jeroen94704/TeensyDSPDAC/dac1.kicad_sch

## KiCad design dac1.kicad_sch (2023-10-21)

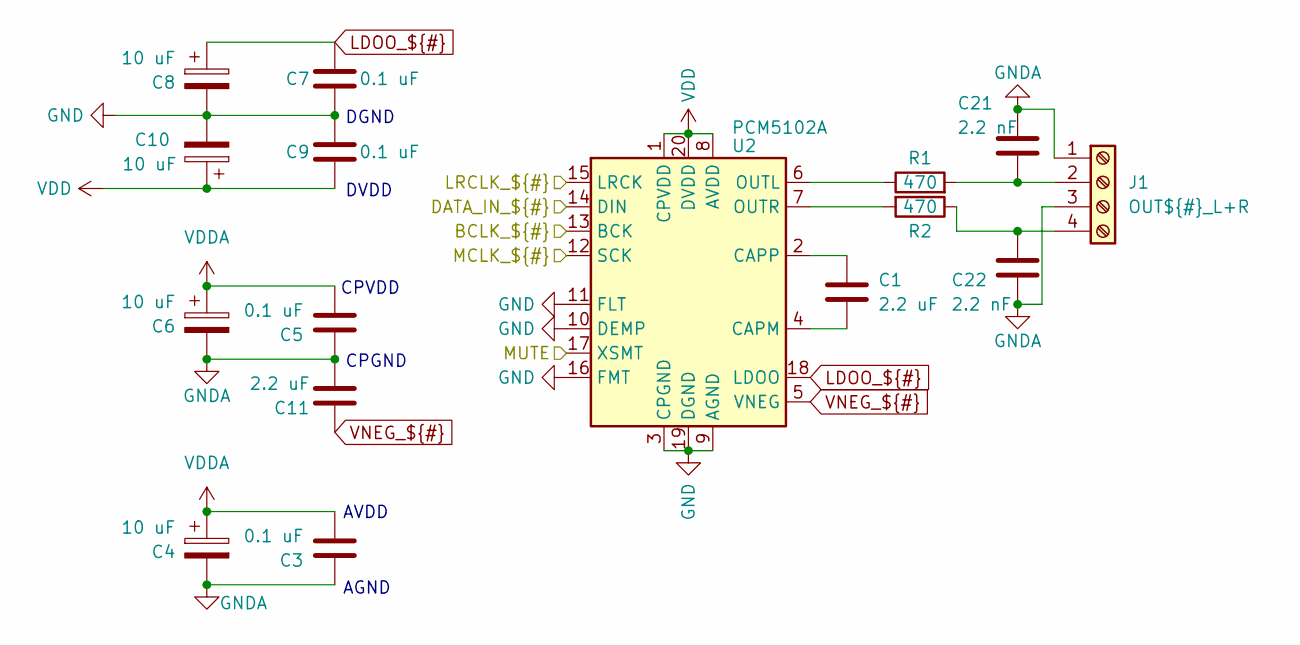
[picture p3: schematic dac1.kicad_sch]

Parts:
C1, C11: 2.2 uF; C_0805_2012Metric_Pad1.18x1.45mm_HandSolder
C3, C5, C7, C9: 0.1 uF; C_0805_2012Metric_Pad1.18x1.45mm_HandSolder
C4, C6, C8, C10: 10 uF; CP_Elec_4x5.4
C21, C22: 2.2 nF; C_0805_2012Metric_Pad1.18x1.45mm_HandSolder
J1: OUT${#}_L+R; TerminalBlock_Phoenix_MKDS-1,5-4-5.08_1x04_P5.08mm_Horizont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
R1, R2: 470; R_0805_2012Metric_Pad1.20x1.40mm_HandSolder
U2: PCM5102A; TSSOP-20_4.4x6.5mm_P0.65mm

Connections:
BCLK_${#}: U2.13 (BCK)
DATA_IN_${#}: U2.14 (DIN)
GND: C7.1, C8.2, C9.2, C10.2, U2.3 (CPGND), U2.9 (AGND), U2.10 (DEMP), U2.11 (FLT), U2.16 (FMT), U2.19 (DGND)
GNDA: C3.1, C4.2, C5.1, C6.2, C11.2, C21.1, C22.2, J1.1, J1.3
LDOO_${#}: C7.2, C8.1, U2.18 (LDOO)
LRCLK_${#}: U2.15 (LRCK)
MCLK_${#}: U2.12 (SCK)
MUTE: U2.17 (XSMT)
unnamed: C1.1, U2.2 (CAPP)
unnamed: C1.2, U2.4 (CAPM)
unnamed: C21.2, J1.2, R1.2
unnamed: C22.1, J1.4, R2.1
unnamed: R1.1, U2.6 (OUTL)
unnamed: R2.2, U2.7 (OUTR)
VDD: C9.1, C10.1, U2.1 (CPVDD), U2.8 (AVDD), U2.20 (DVDD)
VDDA: C3.2, C4.1, C5.2, C6.1
VNEG_${#}: C11.1, U2.5 (VNEG)

Notes on the sheet:
DVDD
CPGND
DGND
AVDD
AGND
CPVDD
