jeroen94704/TeensyDSPDAC/dac2.kicad_sch

## KiCad design dac2.kicad_sch (2023-10-21)

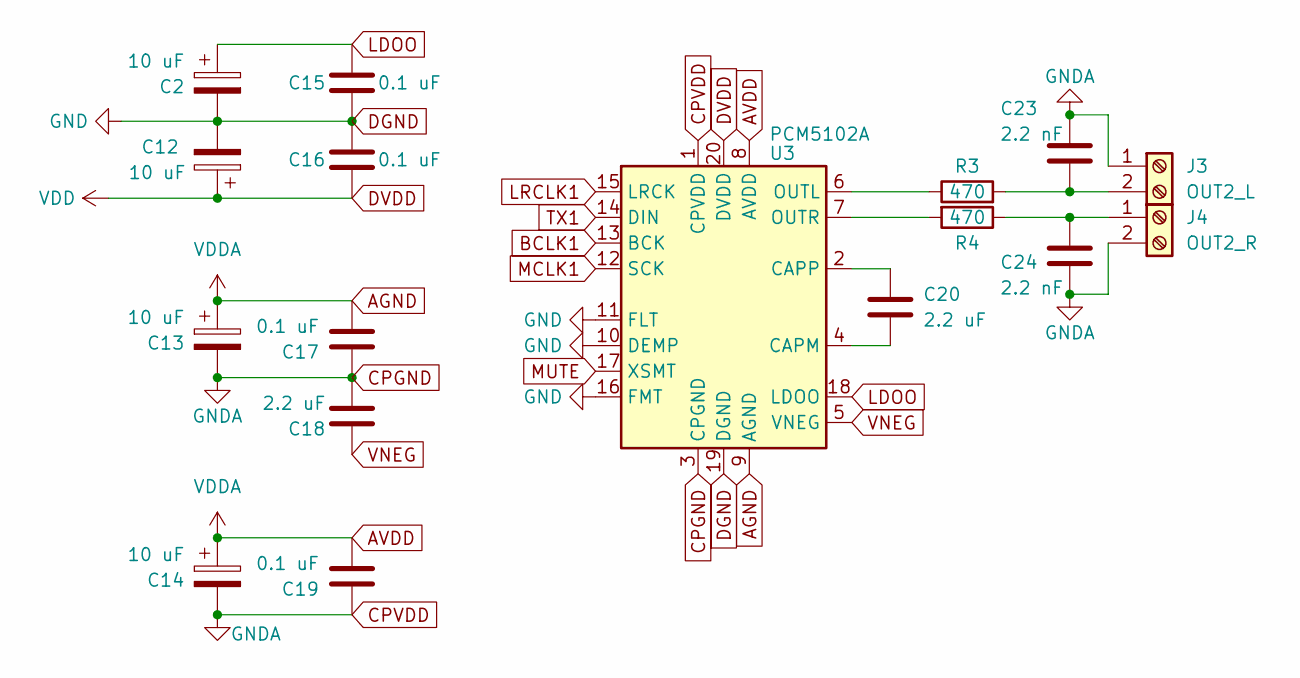
[picture p4: schematic dac2.kicad_sch]

Parts:
C2, C12, C13, C14: 10 uF
C15, C16, C17, C19: 0.1 uF
C18, C20: 2.2 uF
C23, C24: 2.2 nF
J3: OUT2_L
J4: OUT2_R
R3, R4: 470
U3: PCM5102A; TSSOP-20_4.4x6.5mm_P0.65mm

Connections:
AGND: C13.1, C14.1, C17.2, C19.2, U3.8 (AVDD), U3.9 (AGND)
BCLK1: U3.13 (BCK)
CPGND: C13.2, C14.2, C17.1, C18.2, C19.1, C23.1, C24.2, J3.1, J4.2, U3.1 (CPVDD), U3.3 (CPGND)
DGND: C2.2, C12.2, C15.1, C16.2, U3.10 (DEMP), U3.11 (FLT), U3.16 (FMT), U3.19 (DGND)
DVDD: C12.1, C16.1, U3.20 (DVDD)
LDOO: C2.1, C15.2, U3.18 (LDOO)
LRCLK1: U3.15 (LRCK)
MCLK1: U3.12 (SCK)
MUTE: U3.17 (XSMT)
unnamed: C20.1, U3.2 (CAPP)
unnamed: C20.2, U3.4 (CAPM)
unnamed: C23.2, J3.2, R3.2
unnamed: C24.1, J4.1, R4.1
unnamed: R3.1, U3.6 (OUTL)
unnamed: R4.2, U3.7 (OUTR)
TX1: U3.14 (DIN)
VNEG: C18.1, U3.5 (VNEG)
