jeroen94704/TeensyDSPDAC/mcu.kicad_sch

## KiCad design mcu.kicad_sch (2023-11-03)

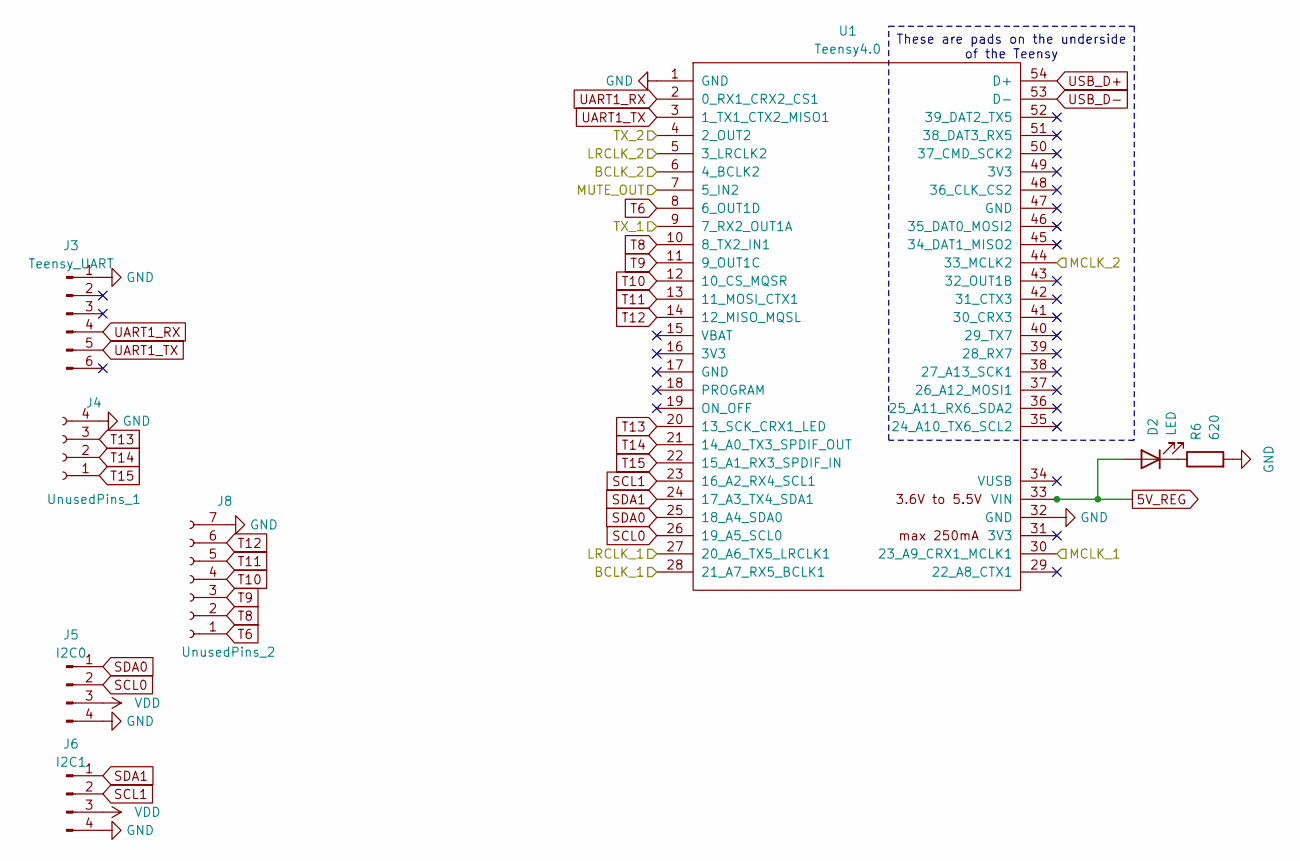
[picture p5: schematic mcu.kicad_sch]

Parts:
D2: LED; LED_0805_2012Metric_Pad1.15x1.40mm_HandSolder
J3: Teensy_UART; PinHeader_1x06_P2.54mm_Vertical
J4: UnusedPins_1; PinSocket_1x04_P2.54mm_Vertical
J5: I2C0; PinSocket_1x04_P2.54mm_Vertical
J6: I2C1; PinSocket_1x04_P2.54mm_Vertical
J8: UnusedPins_2; PinSocket_1x07_P2.54mm_Vertical
R6: 620; R_0805_2012Metric_Pad1.20x1.40mm_HandSolder
U1: Teensy4.0; Teensy40_SMT

Connections:
5V_REG: D2.2 (A), U1.33 (VIN)
BCLK_1: U1.28 (21_A7_RX5_BCLK1)
BCLK_2: U1.6 (4_BCLK2)
GND: J3.1, J4.4, J5.4, J6.4, J8.7, R6.2, U1.1 (GND), U1.32 (GND)
LRCLK_1: U1.27 (20_A6_TX5_LRCLK1)
LRCLK_2: U1.5 (3_LRCLK2)
MCLK_1: U1.30 (23_A9_CRX1_MCLK1)
MCLK_2: U1.44 (33_MCLK2)
MUTE_OUT: U1.7 (5_IN2)
unnamed: D2.1 (K), R6.1
SCL0: J5.2, U1.26 (19_A5_SCL0)
SCL1: J6.2, U1.23 (16_A2_RX4_SCL1)
SDA0: J5.1, U1.25 (18_A4_SDA0)
SDA1: J6.1, U1.24 (17_A3_TX4_SDA1)
T6: J8.1, U1.8 (6_OUT1D)
T8: J8.2, U1.10 (8_TX2_IN1)
T9: J8.3, U1.11 (9_OUT1C)
T10: J8.4, U1.12 (10_CS_MQSR)
T11: J8.5, U1.13 (11_MOSI_CTX1)
T12: J8.6, U1.14 (12_MISO_MQSL)
T13: J4.3, U1.20 (13_SCK_CRX1_LED)
T14: J4.2, U1.21 (14_A0_TX3_SPDIF_OUT)
T15: J4.1, U1.22 (15_A1_RX3_SPDIF_IN)
TX_1: U1.9 (7_RX2_OUT1A)
TX_2: U1.4 (2_OUT2)
UART1_RX: J3.4, U1.2 (0_RX1_CRX2_CS1)
UART1_TX: J3.5, U1.3 (1_TX1_CTX2_MISO1)
USB_D+: U1.54 (D+)
USB_D-: U1.53 (D-)
VDD: J5.3, J6.3

Notes on the sheet:
These are pads on the underside of the Teensy
