jeroen94704/TeensyDSPDAC/mechanical.kicad_sch

## KiCad design mechanical.kicad_sch (2023-10-21)

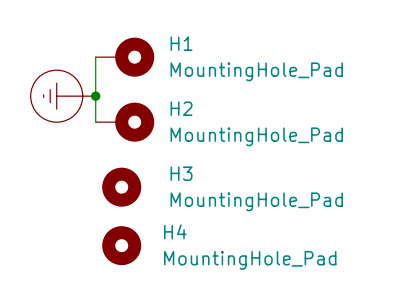
[picture p6: schematic mechanical.kicad_sch]

Parts:
H1, H2: MountingHole_Pad; MountingHole_3.2mm_M3_DIN965_Pad_TopBottom
H3, H4: MountingHole_Pad; MountingHole_3.2mm_M3_DIN965

Connections:
Earth_Protective: H1.1, H2.1
