jeroen94704/TeensyDSPDAC/power.kicad_sch

## KiCad design power.kicad_sch (2023-10-21)

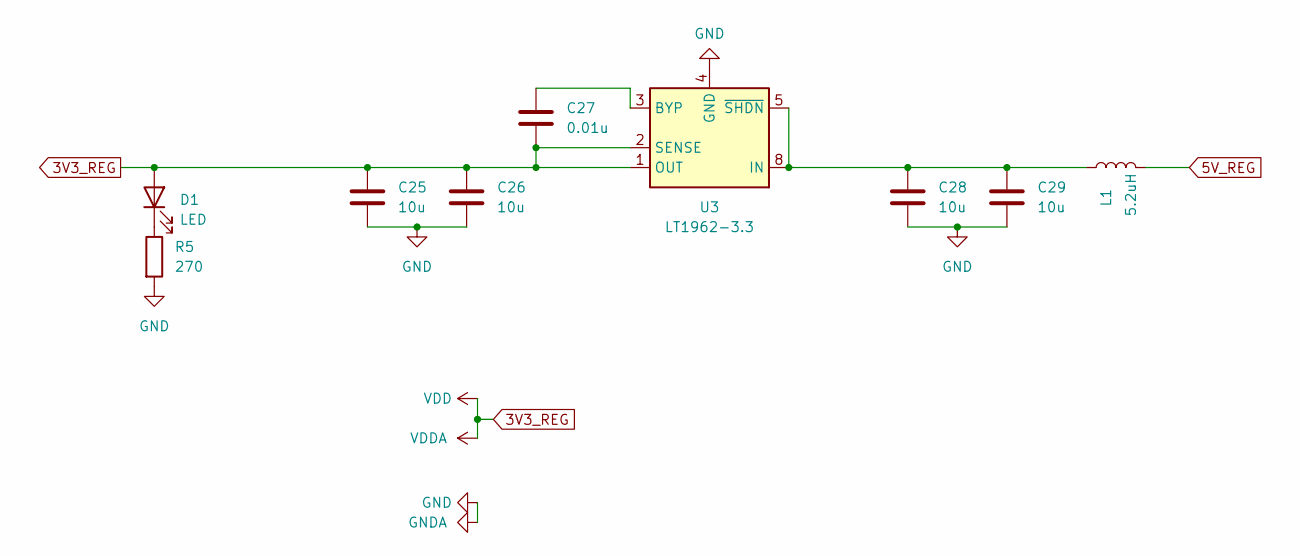
[picture p7: schematic power.kicad_sch]

Parts:
C25, C26, C28, C29: 10u; C_0805_2012Metric_Pad1.18x1.45mm_HandSolder
C27: 0.01u; C_0805_2012Metric_Pad1.18x1.45mm_HandSolder
D1: LED; LED_0805_2012Metric_Pad1.15x1.40mm_HandSolder
L1: 5.2uH; L_10.4x10.4_H4.8
R5: 270; R_0805_2012Metric_Pad1.20x1.40mm_HandSolder
U3: LT1962-3.3; MSOP-8_3x3mm_P0.65mm

Connections:
3V3_REG: C25.1, C26.1, C27.2, D1.2 (A), U3.1 (OUT), U3.2 (SENSE)
5V_REG: L1.2
GND: C25.2, C26.2, C28.2, C29.2, R5.2, U3.4 (GND)
unnamed: C27.1, U3.3 (BYP)
unnamed: C28.1, C29.1, L1.1, U3.5 (~SHDN), U3.8 (IN)
unnamed: D1.1 (K), R5.1
